frahncky/Smart-Metering/hardware/Smart-Metering/3d/Texas_RWU0007A_VQFN-7_2x2mm.step

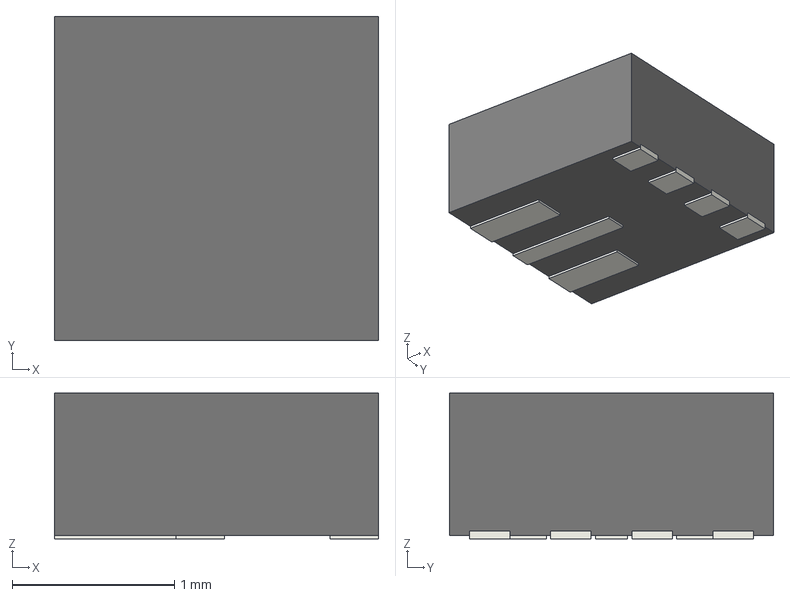
[picture p24: CAD file, 2026-10-04]
hardware/Smart-Metering/3d/Texas_RWU0007A_VQFN-7_2x2mm.step
2.00 x 2.00 x 0.9 mm
corpo
