frahncky/Smart-Metering/modelo 3D/Fusion/historico/exportacao_inicial_20261003_144724/SmartMeter_FrontPanel.step

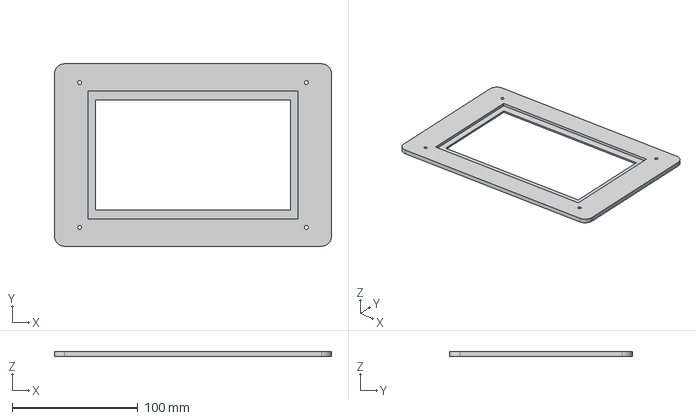
[picture p25: CAD file, 2026-10-04]
modelo 3D/Fusion/historico/exportacao_inicial_20261003_144724/SmartMeter_FrontPanel.step
220.0 x 145.0 x 4.00 mm
