frahncky/Smart-Metering/modelo 3D/Fusion/exportados/20261003_144653_400378/SmartMeter_RearHousing.step

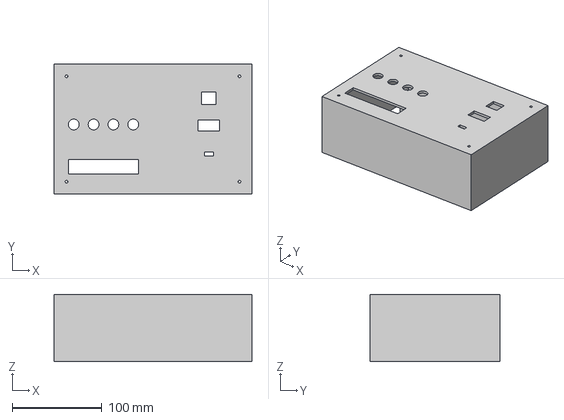
[picture p26: CAD file, 2026-10-04]
modelo 3D/Fusion/exportados/20261003_144653_400378/SmartMeter_RearHousing.step
220.0 x 145.0 x 75.0 mm
