frahncky/Smart-Metering/modelo 3D/Fusion/exportados/20261003_144653_400378/SmartMeter_RearPanel.step

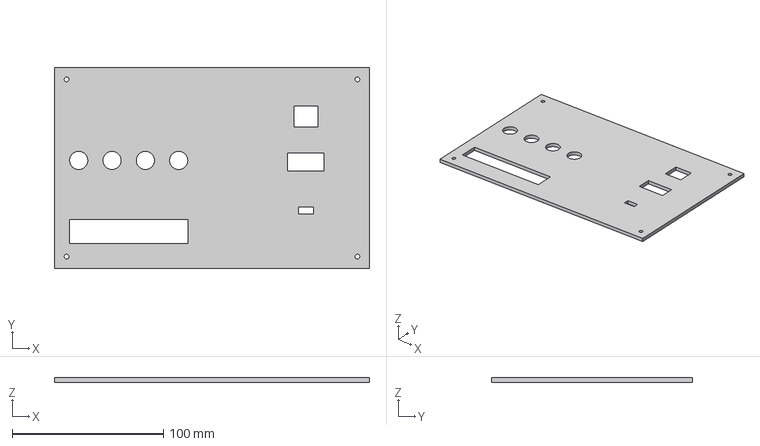
[picture p27: CAD file, 2026-10-04]
modelo 3D/Fusion/exportados/20261003_144653_400378/SmartMeter_RearPanel.step
208.0 x 133.0 x 3.00 mm
